kholia/Light-Intuitive-Digital-Interface/images/Final Values (20 kHz) - Screenshot_2021-01-05_13-51-03.png

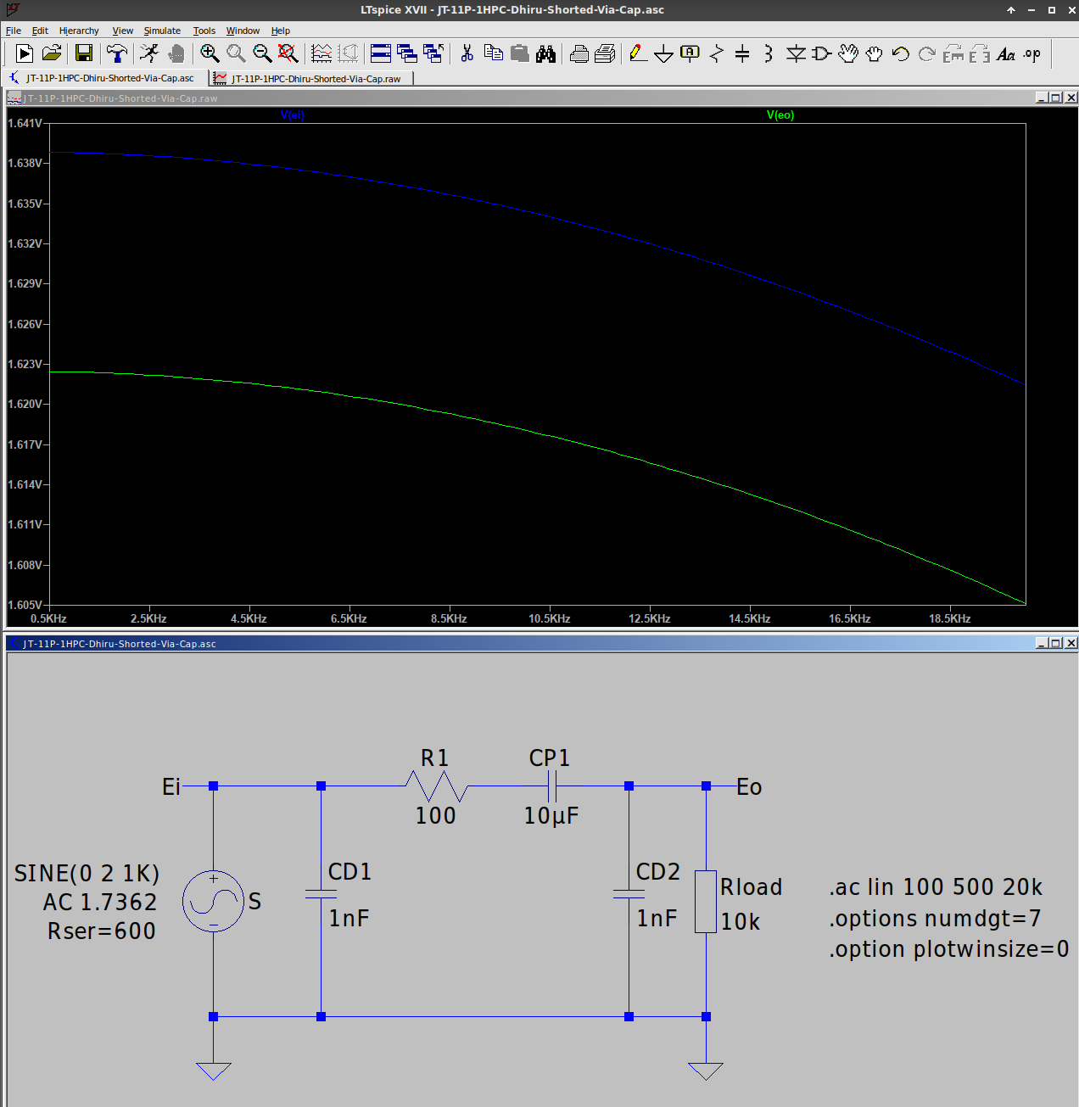
images/Final Values (20 kHz) - Screenshot_2021-01-05_13-51-03.png
