kholia/Light-Intuitive-Digital-Interface/images/Final Values - Screenshot_2021-01-05_12-11-56.png

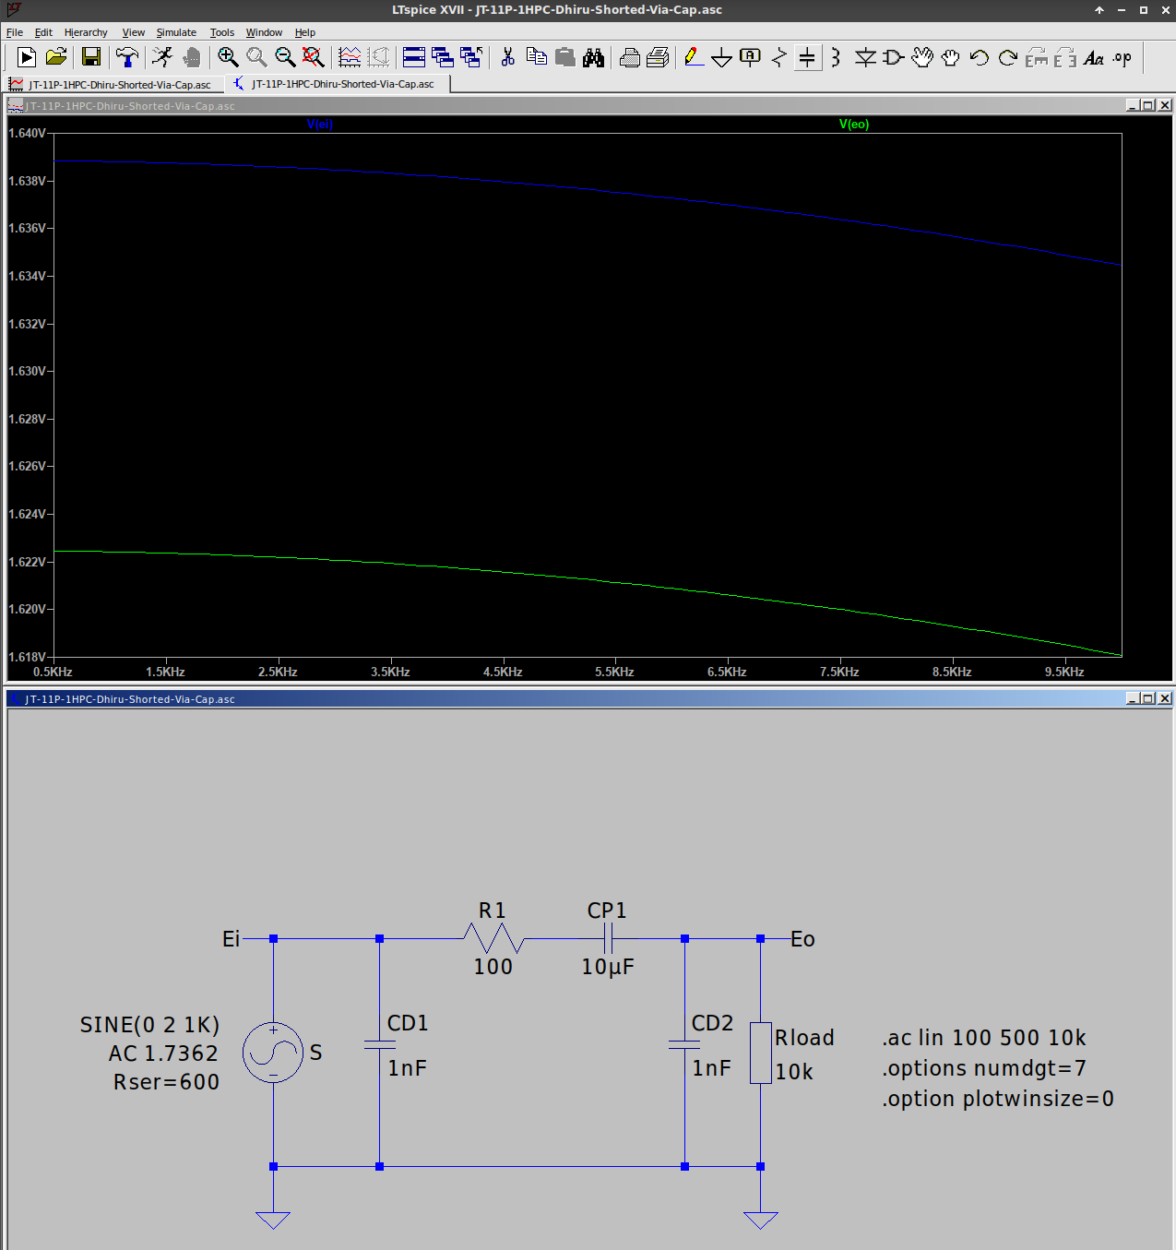
images/Final Values - Screenshot_2021-01-05_12-11-56.png
