kholia/Light-Intuitive-Digital-Interface/images/LiDi v2 - Screenshot_2021-05-29_09-44-15.png

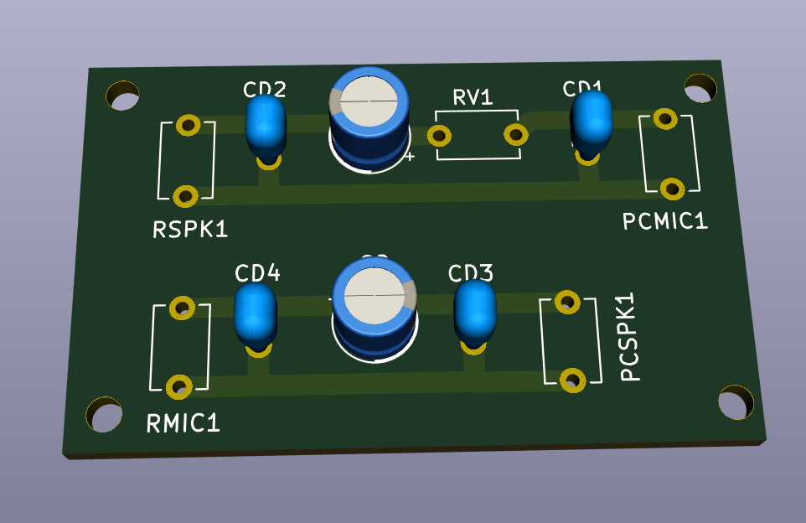
images/LiDi v2 - Screenshot_2021-05-29_09-44-15.png
