kholia/Light-Intuitive-Digital-Interface/images/Me going to US with LiDi v2 - Screenshot_2021-01-05_18-36-41.png

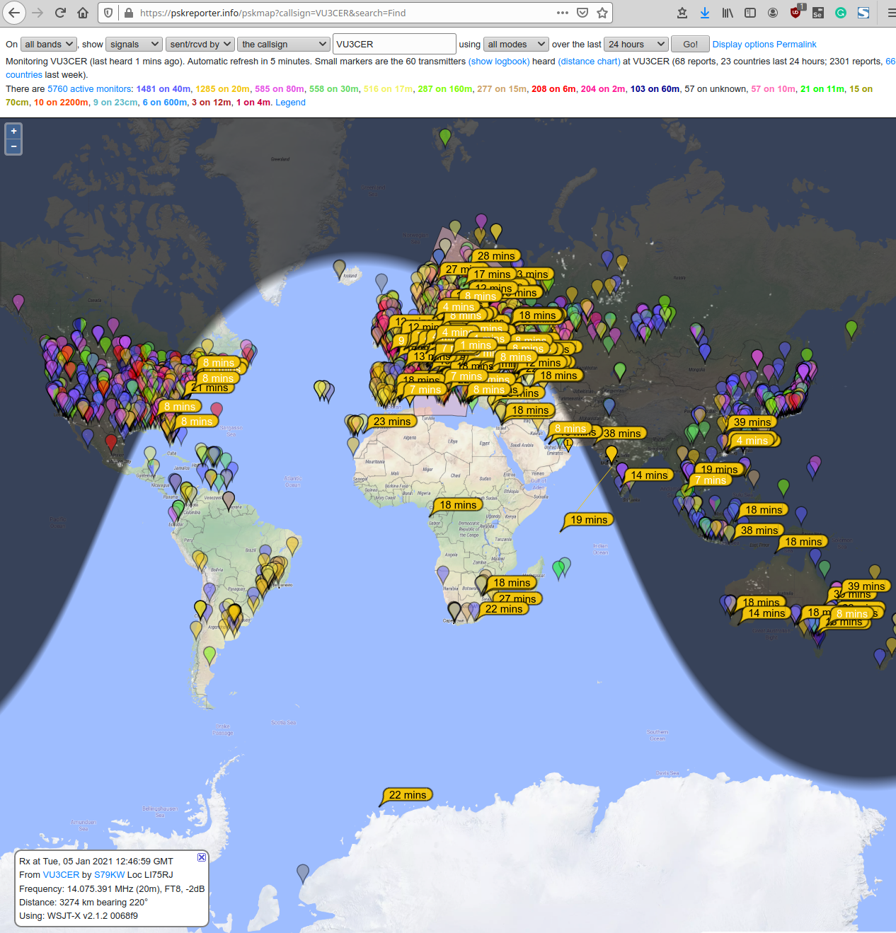
images/Me going to US with LiDi v2 - Screenshot_2021-01-05_18-36-41.png
