kholia/Light-Intuitive-Digital-Interface/images/Screenshot_2020-12-27_16-10-23.png

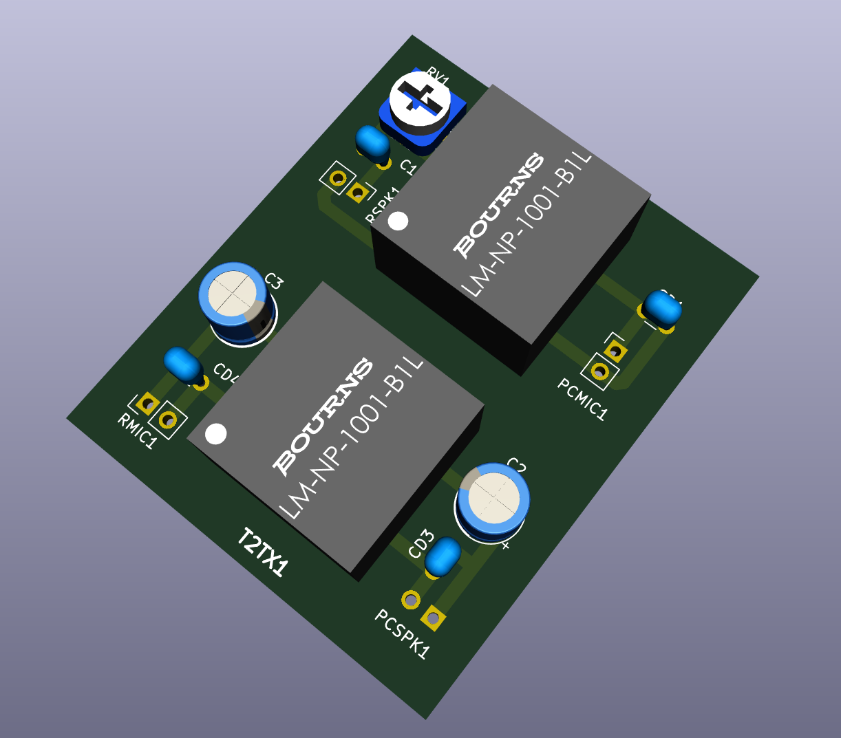
images/Screenshot_2020-12-27_16-10-23.png
