kholia/Light-Intuitive-Digital-Interface/LiDi-Simulation/1uF RC Low-Pass Filter - Screenshot_2020-12-29_18-02-39.png

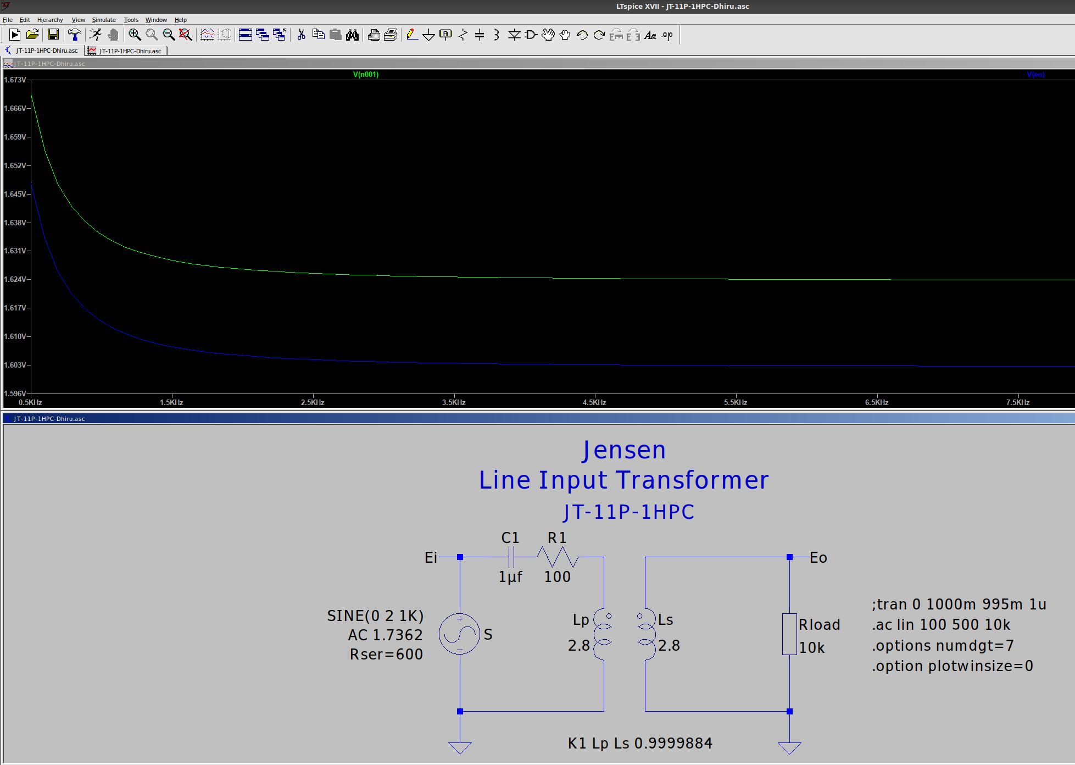
LiDi-Simulation/1uF RC Low-Pass Filter - Screenshot_2020-12-29_18-02-39.png
