kholia/Light-Intuitive-Digital-Interface/LiDi-Simulation/100nF 100R (best) - Screenshot_2020-12-29_18-05-08.png

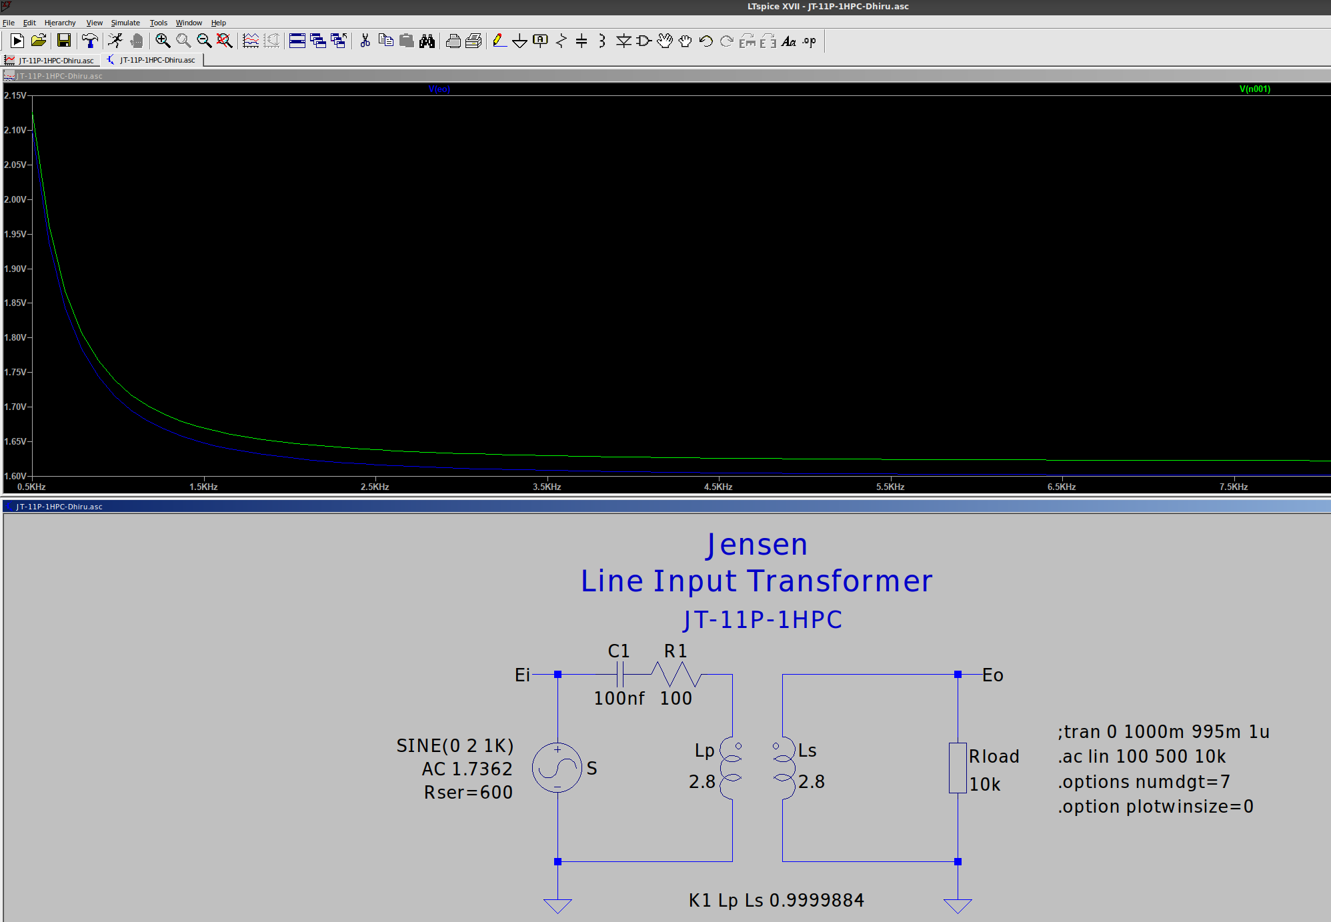
LiDi-Simulation/100nF 100R (best) - Screenshot_2020-12-29_18-05-08.png
