kholia/Light-Intuitive-Digital-Interface/LiDi-Simulation/100nF - Parametric resistor - Screenshot_2020-12-29_19-04-52.png

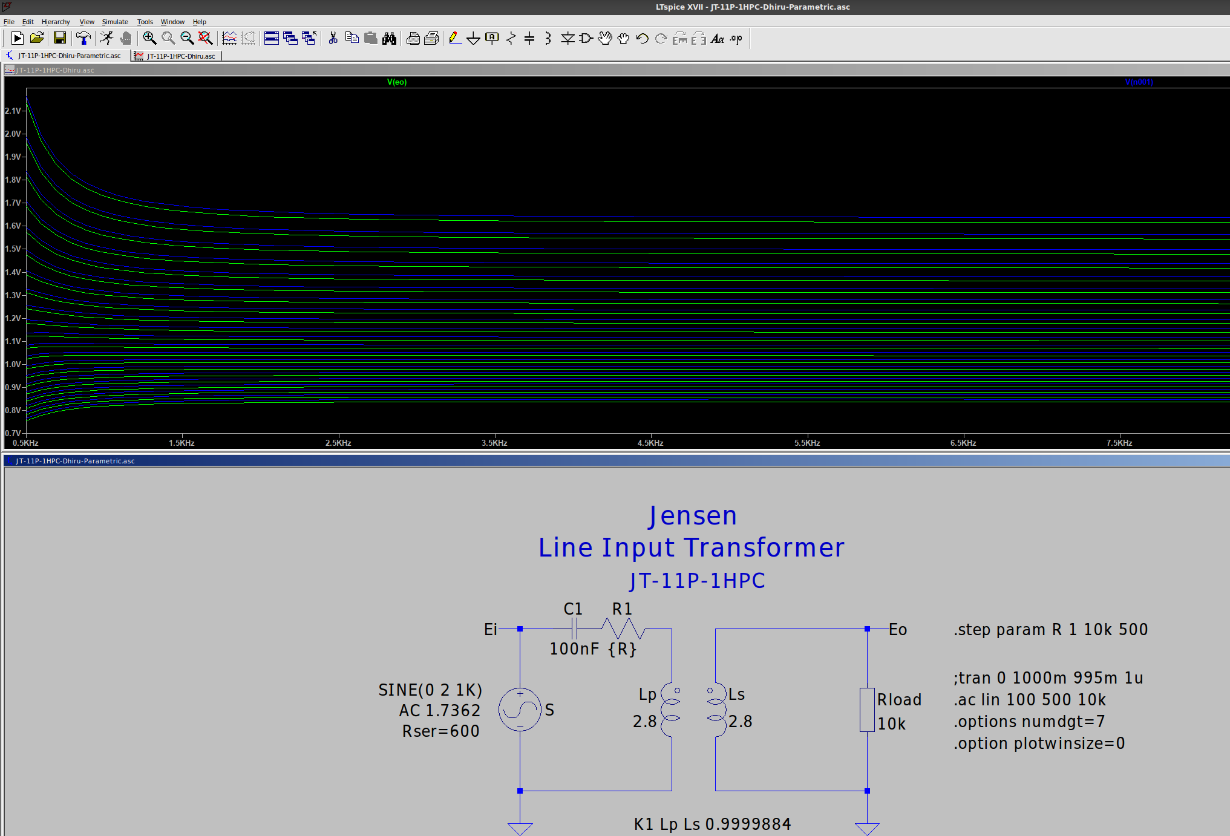
LiDi-Simulation/100nF - Parametric resistor - Screenshot_2020-12-29_19-04-52.png
