kholia/Light-Intuitive-Digital-Interface/LiDi-Simulation/100nF - phase also OK - Screenshot_2020-12-29_18-34-01.png

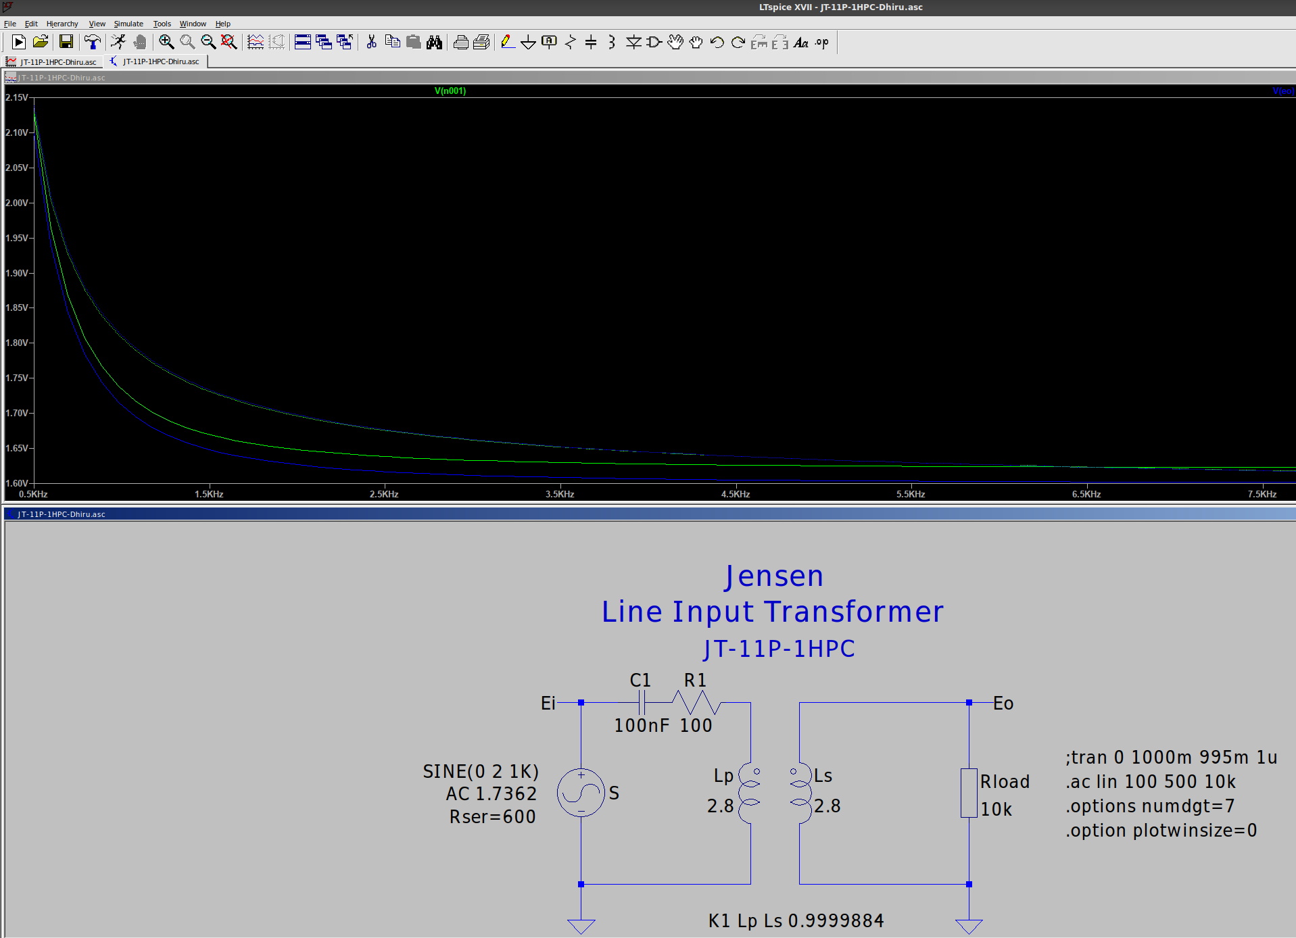
LiDi-Simulation/100nF - phase also OK - Screenshot_2020-12-29_18-34-01.png
