kholia/Light-Intuitive-Digital-Interface/LiDi-Simulation/JT-11P-1HPC.GIF

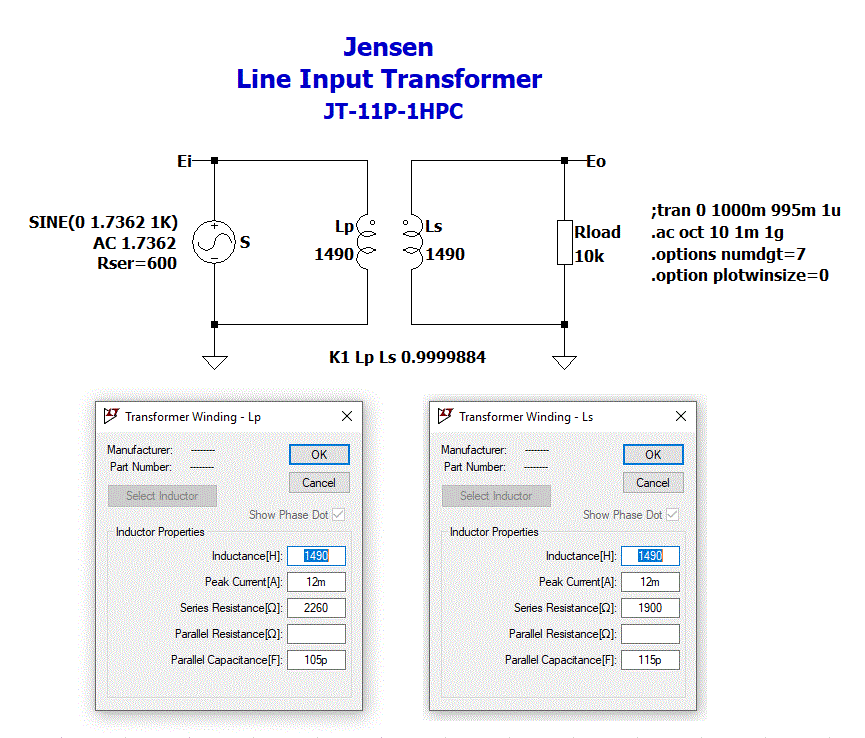
LiDi-Simulation/JT-11P-1HPC.GIF
