kholia/Light-Intuitive-Digital-Interface/LiDi-Simulation/Plain Transformer Graph - Screenshot_2020-12-29_17-36-35.png

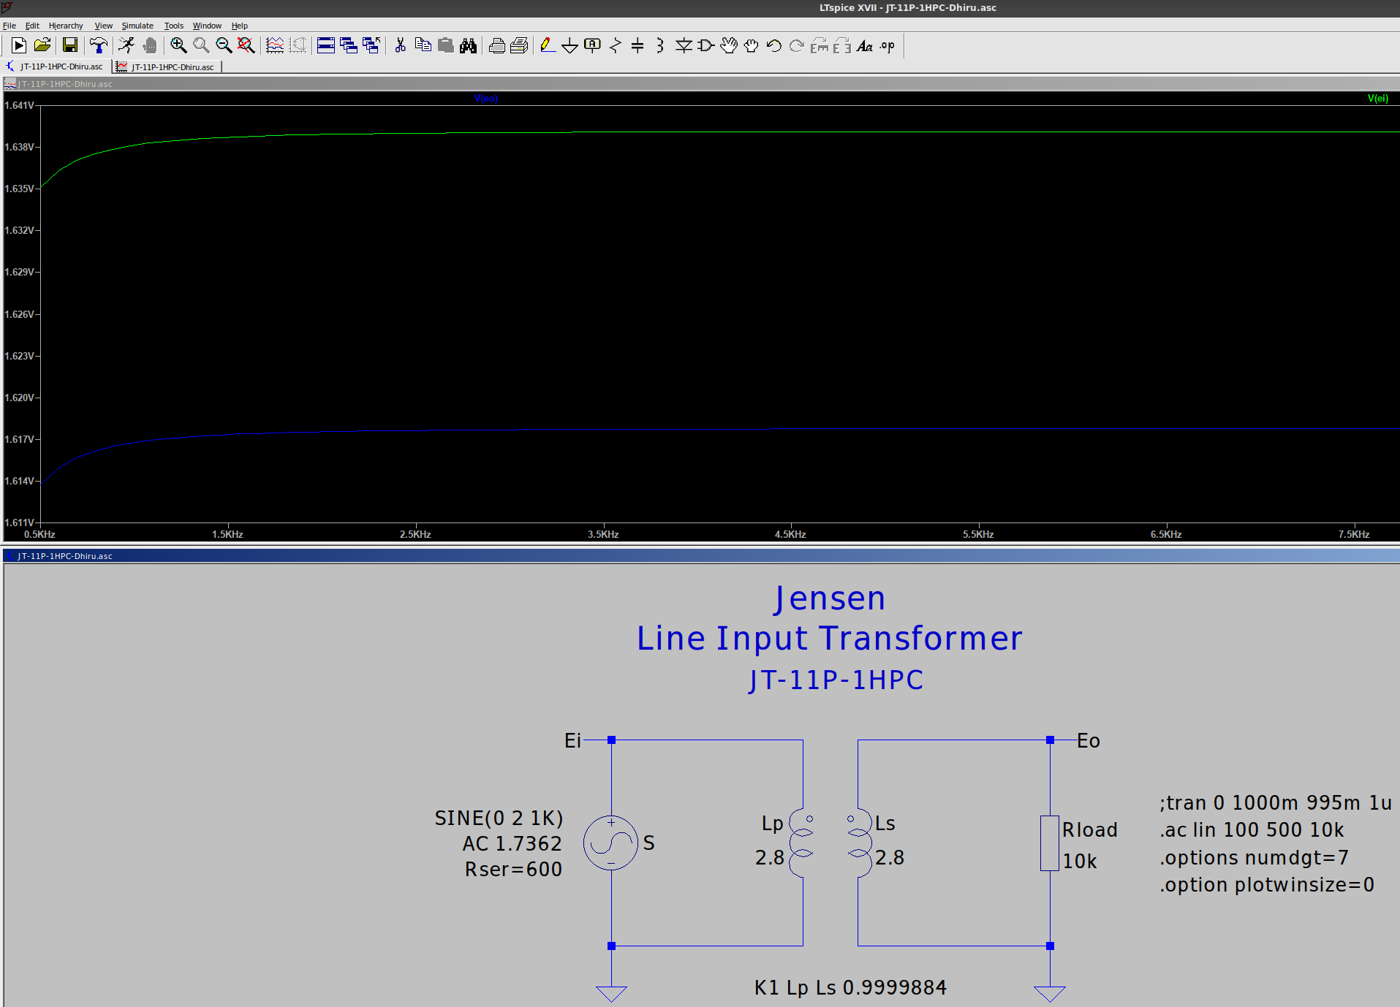
LiDi-Simulation/Plain Transformer Graph - Screenshot_2020-12-29_17-36-35.png
