kholia/Light-Intuitive-Digital-Interface/LiDi-Simulation/Resistor Removed - Screenshot_2020-12-29_18-17-48.png

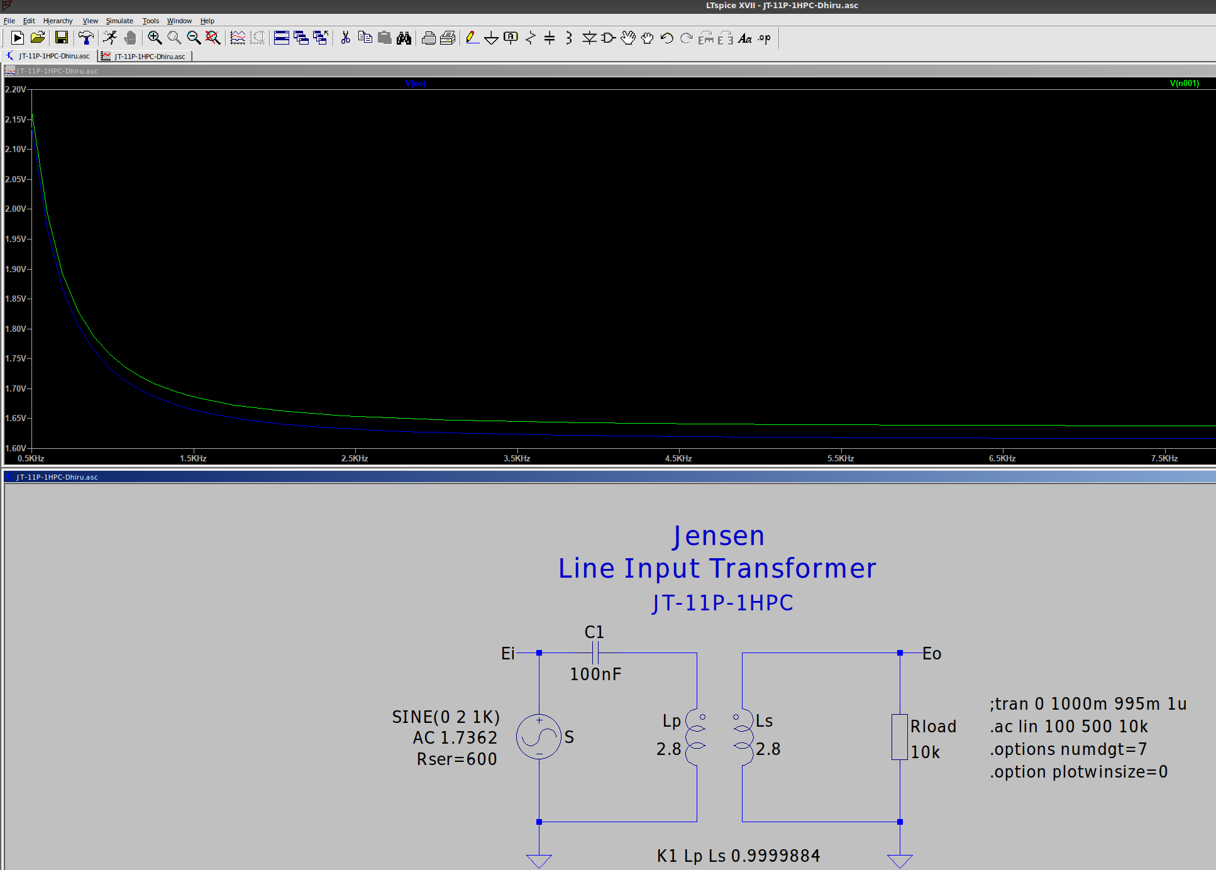
LiDi-Simulation/Resistor Removed - Screenshot_2020-12-29_18-17-48.png
