kholia/Light-Intuitive-Digital-Interface/LiDi-Simulation/DuinoVox.asc

C1: cap; 2.2µF
C2: cap; 220nf
D1: schottky; 1N4148
Q1: npn; 2N2222A
R1: res; 22k
R2: res; 6.8k
R3: res; 10k
R4: res; 1k
R5: res; 470k
V1: voltage; 5; Rser=.1
V2: signal; SINE(0 .1 440 0 0 0 200)
Named nets: 0, Vcc, IN, OUT, BASE, Q1
.tran 1
.model 1N4001 D(Is=14.11n N=1.984 Rs=33.89m Ikf=94.81 Xti=3 Eg=1.11 Cjo=25.89p M=.44 Vj=.3245 Fc=.5 Bv=75 Ibv=10u Tt=5.7u Iave=1 Vpk=50 mfg=GI type=silicon)
*ZETEX  2N2222A Spice model   Last revision 9/12/92
*
.MODEL 2N2222A NPN IS =3.0611E-14 NF =1.00124 BF =220 IKF=0.52 
+              VAF=104 ISE=7.5E-15 NE =1.41 NR =1.005 BR =4 IKR=0.24 
+              VAR=28 ISC=1.06525E-11 NC =1.3728 RB =0.13 RE =0.22 
+              RC =0.12 CJC=9.12E-12 MJC=0.3508 VJC=0.4089 
+              CJE=27.01E-12 TF =0.325E-9 TR =100E-9
*
*
*                          (C)  1992 ZETEX PLC
*
*   The copyright in this model  and  the design embodied belong to
*   Zetex PLC ("Zetex"). It is supplied free of charge by Zetex for
*   the purpose  of research  and design  and may be used or copied
*   intact (including this notice) for that purpose only. All other
*   rights  are  reserved.  The model  is believed  accurate but no
*   condition or warranty as to its  merchantability or fitness for
*   purpose  is  given  and  no liability  in respect of any use is
*   accepted by Zetex PLC, its distributors or agents.
*
*
*   Zetex PLC, Fields New Road, Chadderton, Oldham  OL9 8NP
