kholia/Light-Intuitive-Digital-Interface/LiDi-Simulation/JT-11P-1HPC-Dhiru-Shorted-Via-Cap.asc

CD1: cap; 1nF
CD2: cap; 1nF
CP1: cap; 10µF
R1: res; 100
Rload: EuropeanResistor; 10k
S: signal; SINE(0 2 1K); AC 1.7362; Rser=600
Named nets: 0, Eo, Ei
.ac lin 100 500 10k
.option plotwinsize=0
.options numdgt=7
