kholia/Light-Intuitive-Digital-Interface/LiDi-Simulation/JT-11P-1HPC-Dhiru.asc

C1: cap; 100nF
Lp: ind2; 2.8; Ipk=12m Rser=66 Cpar=105p
Ls: ind2; 2.8; Ipk=12m Rser=66 Cpar=115p
R1: res; 5k
Rload: EuropeanResistor; 10k
S: signal; SINE(10 2 1K); AC 1.7362; Rser=600
Named nets: 0, Eo, Ei
K1 Lp Ls 0.9999884
.ac lin 100 500 10k
Jensen
Line Input Transformer
JT-11P-1HPC
;tran 0 1000m 995m 1u
.option plotwinsize=0
.options numdgt=7
