kholia/Light-Intuitive-Digital-Interface/LiDi-Simulation/JT-11P-1HPC.asc

Lp: ind2; 1490; Ipk=12m Rser=2260 Cpar=105p
Ls: ind2; 1490; Ipk=12m Rser=1900 Cpar=115p
Rload: EuropeanResistor; 10k
S: signal; SINE(0 1.7362 1K); AC 1.7362; Rser=600
Named nets: 0, Eo, Ei
K1 Lp Ls 0.9999884
.ac oct 10 1m 1g
Jensen
Line Input Transformer
JT-11P-1HPC
;tran 0 1000m 995m 1u
.option plotwinsize=0
.options numdgt=7
